nomand/EachineVR006/Images/00.jpg

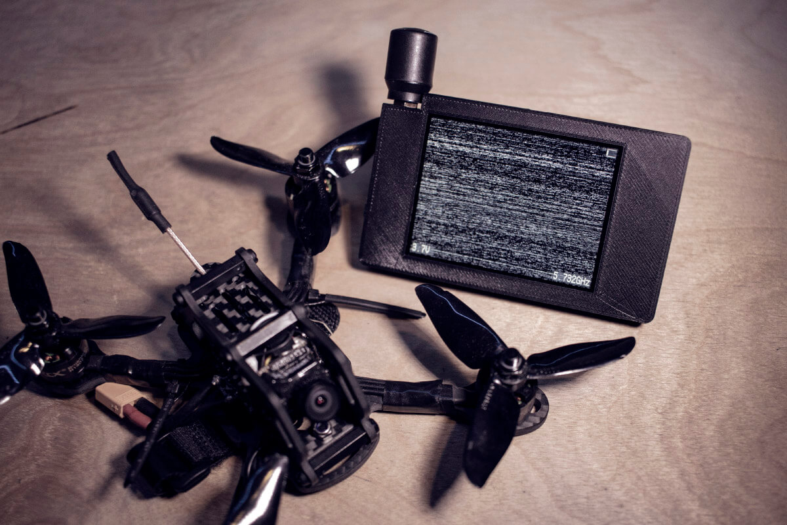
Images/00.jpg
